markpatterson27/Project-Hand-Sanitiser-Level-Monitor/mp-tests/stubs/machine.py

"""
The purpose of this module is to emulate the machine module of the ESP32 chip.  The primary reason to 
emulate the chip is for test-driving code (TDD).

Verified Firmware version: esp32-20190610-v1.11-37-g62f004ba4

Portions also tested with esp8266-20190529-v1.11
"""
import time

EMULATION_MODE = True

__author__ = 'Todd Flanders https://github.com/tflander/Esp32IotKata'

expectedPulseTimeForTesting = 0
expectedPulseTimeErrorForTesting = None
expectedTimeSleepMs = []
expectedTimeSleepUs = []
reset_called_for_testing = False

def resetExpectationsForTesting():
    global expectedPulseTimeForTesting
    global expectedPulseTimeErrorForTesting
    global expectedTimeSleepMs
    global expectedTimeSleepUs
    global reset_called_for_testing

    expectedPulseTimeForTesting = 0
    expectedPulseTimeErrorForTesting = None
    expectedTimeSleepMs = []
    expectedTimeSleepUs = []
    reset_called_for_testing = False


# noinspection PyUnusedLocal,PyUnusedLocal,PyUnusedLocal
def time_pulse_us(pin, pulse_level, timeout_us):
    global expectedPulseTimeErrorForTesting
    if expectedPulseTimeErrorForTesting is not None:
        raise expectedPulseTimeErrorForTesting  # pylint: disable=raising-bad-type

    try:
        pulse_time = expectedPulseTimeForTesting.pop(0)
    except:
        pulse_time = expectedPulseTimeForTesting

    if type(pulse_time) == int:
        return pulse_time
    else:
        if not pulse_time:
            raise Exception("unexpected call to time_pulse_us on empty expectation list")
        raise pulse_time


def reset():
    global reset_called_for_testing
    reset_called_for_testing = True


def sleep_us_for_monkey_patching(delayUs):
    time.sleep(delayUs / 1000000)
    expectedTimeSleepUs.append(delayUs)


def sleep_ms_for_monkey_patching(delayMs):
    time.sleep(delayMs / 1000)
    expectedTimeSleepMs.append(delayMs)


time.sleep_us = sleep_us_for_monkey_patching
time.sleep_ms = sleep_ms_for_monkey_patching


def unique_id():
    # return '000000'
    return bytes(6)


class Pin:
    IN = "in"
    OUT = "out"

    def resetExpectationsForTesting(self):
        self.triggerValuesForTesting = []

    # noinspection PyUnusedLocal,PyUnusedLocal
    def __init__(self, pin, mode=OUT, pull=None, value=0):
        self.currentStateForTesting = None
        self.currentStateForTesting = 1
        self.currentStateForTesting = None
        self.pinForTesting = pin
        self.triggerValuesForTesting = []
        self.resetExpectationsForTesting()
        self.value(value)

    def on(self):
        self.currentStateForTesting = 1
        self.triggerValuesForTesting.append(self.currentStateForTesting)

    def off(self):
        self.currentStateForTesting = 0
        self.triggerValuesForTesting.append(self.currentStateForTesting)

    def value(self, newValue=None):
        if newValue == 0:
            self.off()
        elif newValue == 1:
            self.on()
        if self.currentStateForTesting is None:
            raise Exception("Checking Value of Uninitialized OUT Pin.  Set the value before checking.")
        return self.currentStateForTesting


class Timer:

    PERIODIC = 0

    def __init__(self, id):
        self.timer_id_for_testing = id
        self.is_running_for_testing = False

    def deinit(self):
        self.is_running_for_testing = False

    def init(self, period, mode=PERIODIC, callback=None):
        self.is_running_for_testing = True


class ADC:

    ATTN_11DB = "attenuate 11DB"

    def __init__(self, pin):
        self.pinForTesting = pin

    def atten(self, attenuation):
        self.attenForTesting = attenuation
        # print("TEST: ", attenuation)

    def read(self):
        return 200

class TouchPad:

    def __init__(self, pinObj):
        self.pinObjectForTesting = pinObj

    def read(self):
        return 200

class RTC(object):

    def __init__ (self):
        self._memory = b''

    # @property
    def memory(self):
        return self._memory

    # @memory.setter
    def memory(self, value):
        self._memory = value
